queengooborg/BambuTagger-AMS-C/src/web_server.h

#pragma once

#include <Arduino.h>
#include <WiFi.h>
#include <WebServer.h>
#include <ArduinoJson.h>
#include "config.h"
#include "rfid_manager.h"
#include "bambu_printer.h"

class WebInterface {
 public:
  void begin(SystemConfig& cfg, RfidManager* rfid, BambuPrinter* printer,
             void (*rebootCallback)(void) = nullptr, void (*otaCallback)(void) = nullptr);
  void handleClient();
  void updateStatus(bool wifiConnected, const char* ipAddress, bool mqttConnected,
                    bool printerOnline);

 private:
  void handleRoot();
  void handleFavicon();
  void handleStatus();
  void handleAmsStatus();
  void handleConfigGet();
  void handleConfigPost();
  void handleScan();
  void handleSend();
  void handleSync();
  void handleOta();
  void handleOtaCheck();
  void handleAmsGetRfid();
  void handleVersion();
  void handleLedGet();
  void handleLedPost();
  void sendJsonResponse(JsonDocument& doc, int code = 200);
  void setupRoutes();

  WebServer* server;
  SystemConfig* config;
  RfidManager* rfidManager;
  BambuPrinter* bambuPrinter;
  void (*rebootFn)(void);
  void (*otaFn)(void);

  bool wifiStatus;
  String ipAddress;
  bool mqttStatus;
  bool printerOnlineStatus;
};
